leboeuf-dup/Track-Counter/images/photo2.jpg

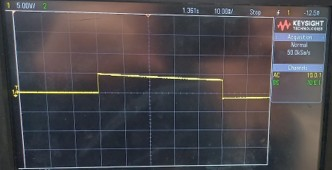
images/photo2.jpg
